svofski/lepetomane-ringard/sw/pico/reset.c

#include "pico/bootrom.h"
#include "tusb.h"

// Support for default BOOTSEL reset by changing baud rate
void tud_cdc_line_coding_cb(__unused uint8_t itf, cdc_line_coding_t const* p_line_coding) {
    if (p_line_coding->bit_rate == PICO_STDIO_USB_RESET_MAGIC_BAUD_RATE) {
        reset_usb_boot(0u, 0u);
    }
}
